Xchiliarch/flatbox_RGB-OLED/img/sketch.png

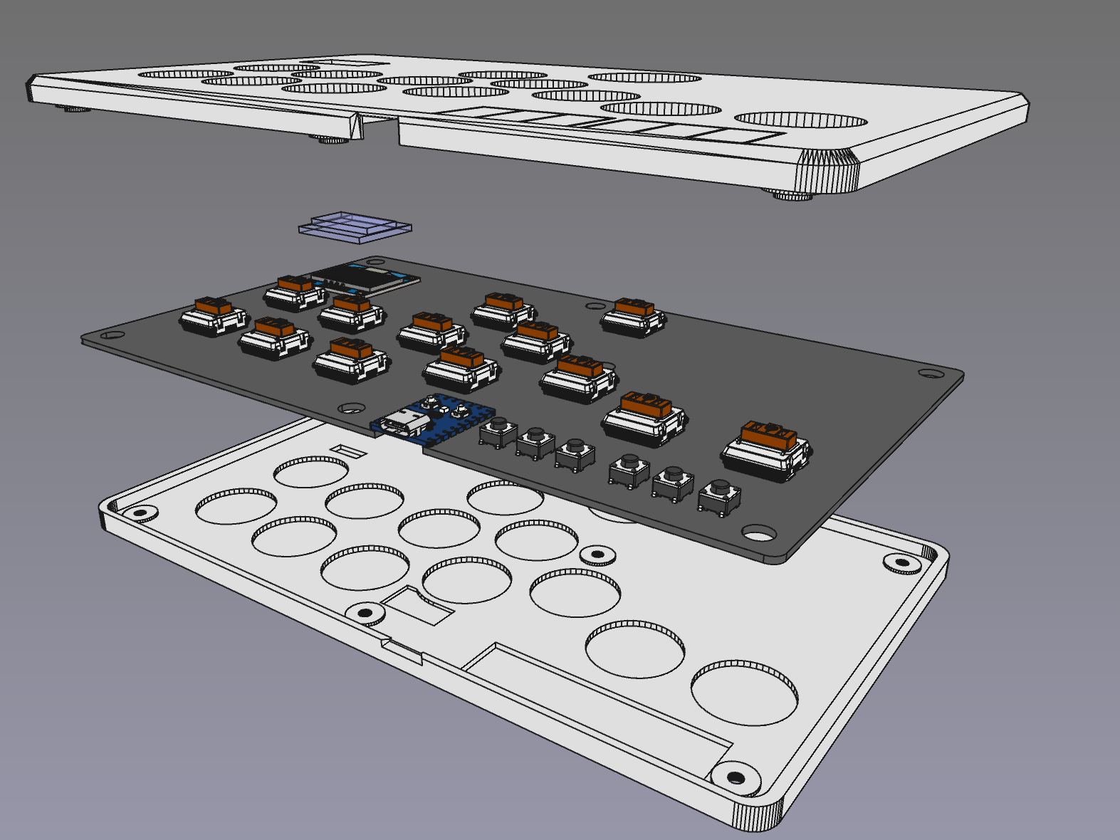
img/sketch.png
